CapibaraZero/resources/electrical_diagram/Arduino_Nano_ESP32/Navigation_board.png

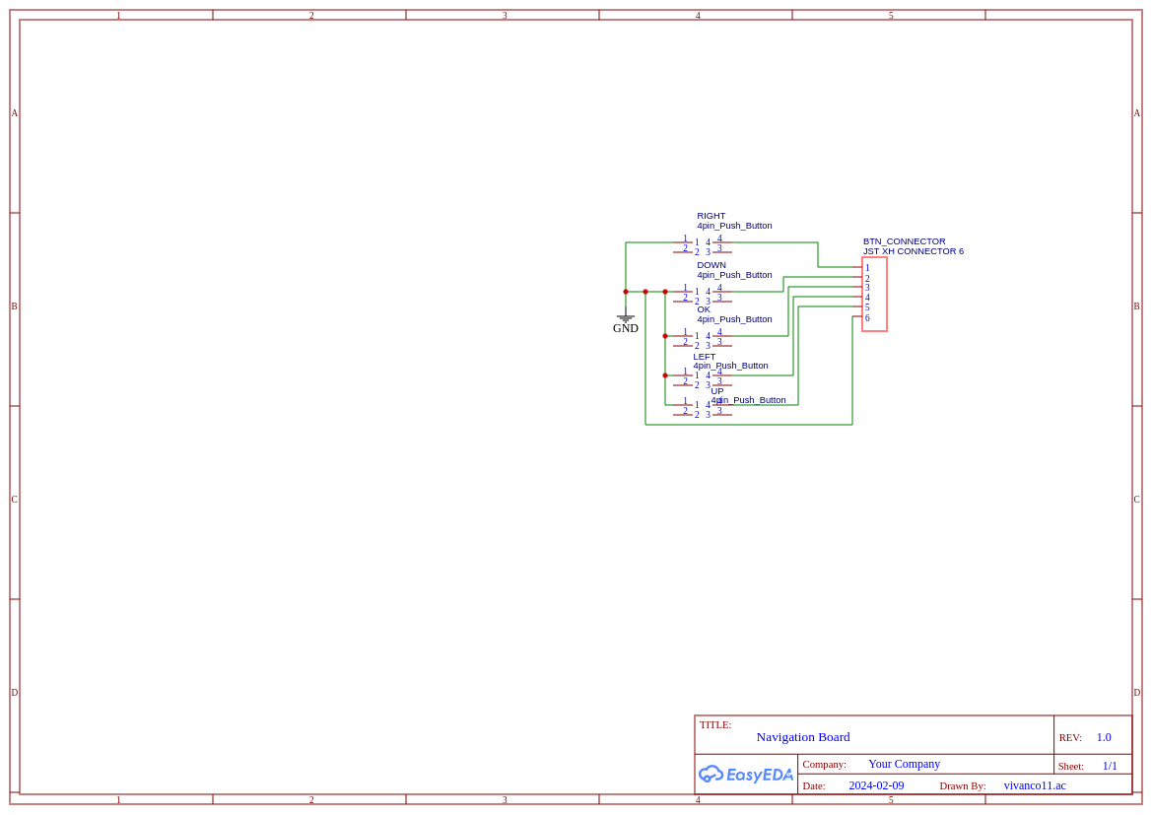
electrical_diagram/Arduino_Nano_ESP32/Navigation_board.png
